ElKatzchen/6DOF-3D-Printed-Robotic-Arm-ROS-2-Computer-Vision-Integration/3D-Printed_Files/SG90S/Pieces/Arm_1st_Joint.SLDPRT

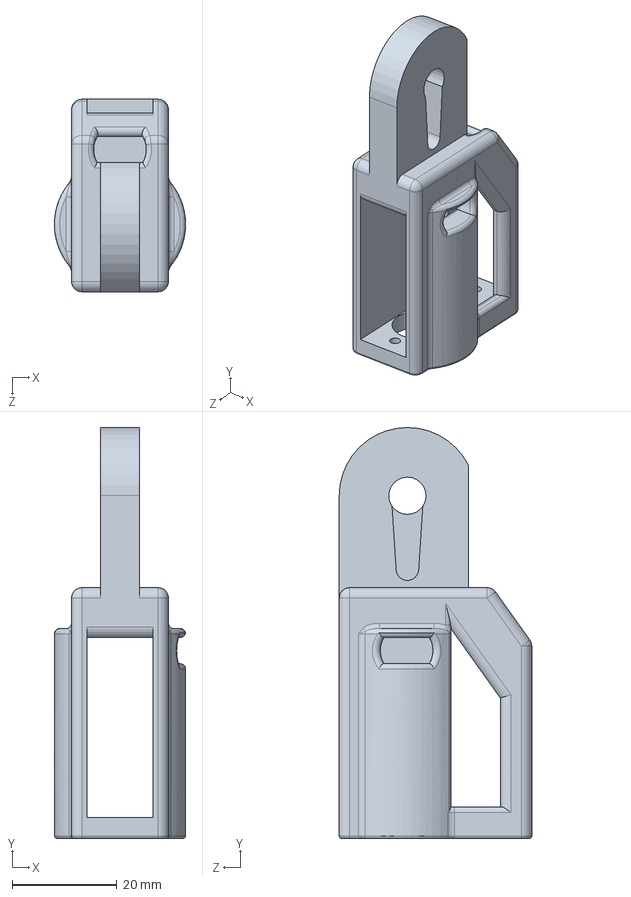
[picture p12: CAD file, 2026-02-13]
3D-Printed_Files/SG90S/Pieces/Arm_1st_Joint.SLDPRT
25.0 x 78.3 x 36.7 mm
