ElKatzchen/6DOF-3D-Printed-Robotic-Arm-ROS-2-Computer-Vision-Integration/3D-Printed_Files/SG90S/STLs/Arm_2nd_Joint.STL

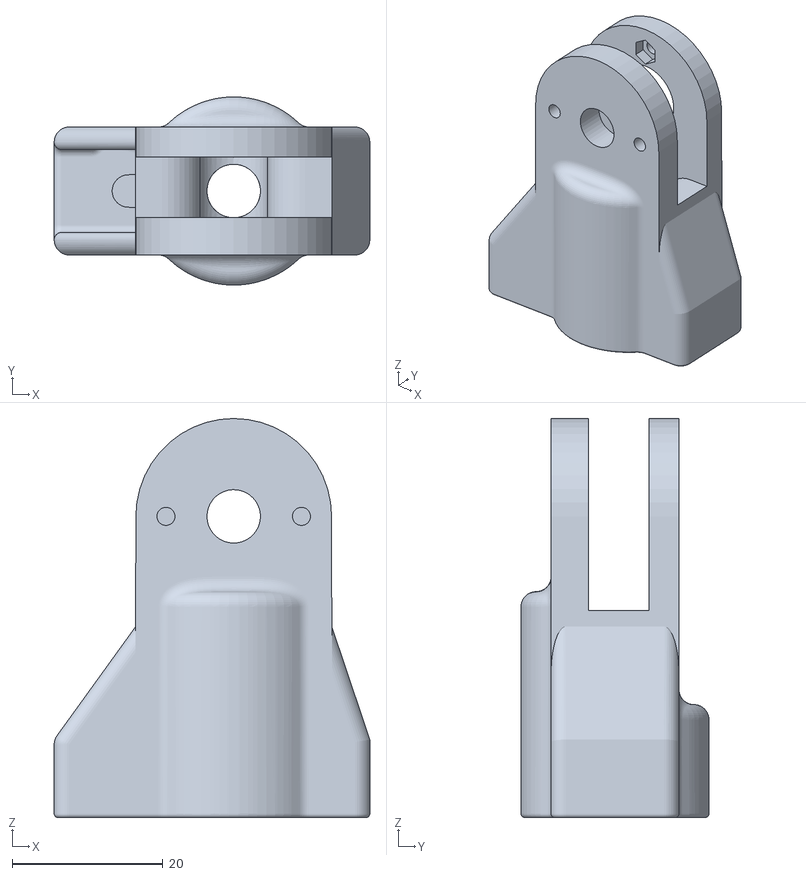
[picture p13: CAD file, 2026-02-13]
3D-Printed_Files/SG90S/STLs/Arm_2nd_Joint.STL
41.9 x 25.0 x 53.0
