ElKatzchen/6DOF-3D-Printed-Robotic-Arm-ROS-2-Computer-Vision-Integration/3D-Printed_Files/ES08MA_II/Pieces/Arm_2nd_Joint.SLDPRT

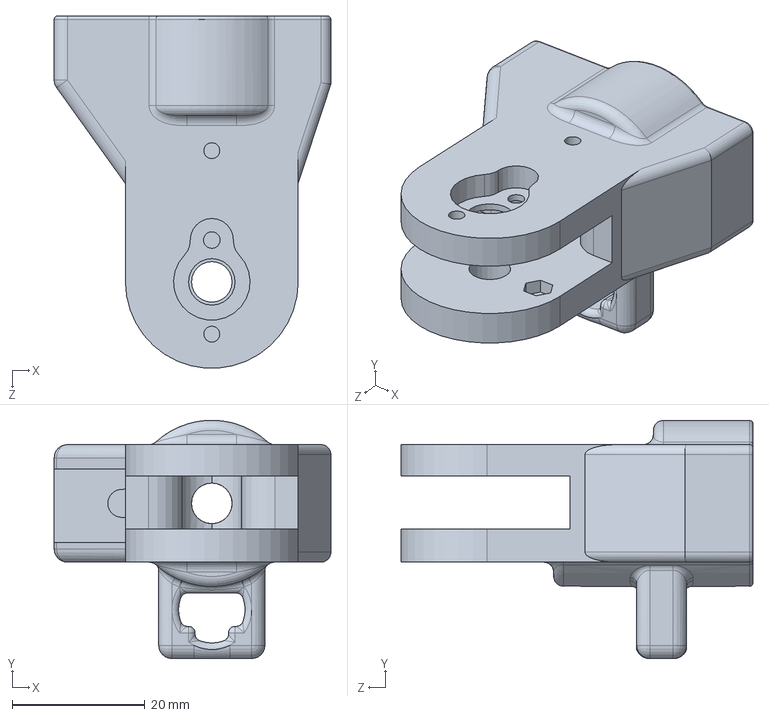
[picture p14: CAD file, 2026-04-28]
3D-Printed_Files/ES08MA_II/Pieces/Arm_2nd_Joint.SLDPRT
41.6 x 35.8 x 53.0 mm
