ElKatzchen/6DOF-3D-Printed-Robotic-Arm-ROS-2-Computer-Vision-Integration/3D-Printed_Files/SG90S/Pieces/Base_Arm_Joint.SLDPRT

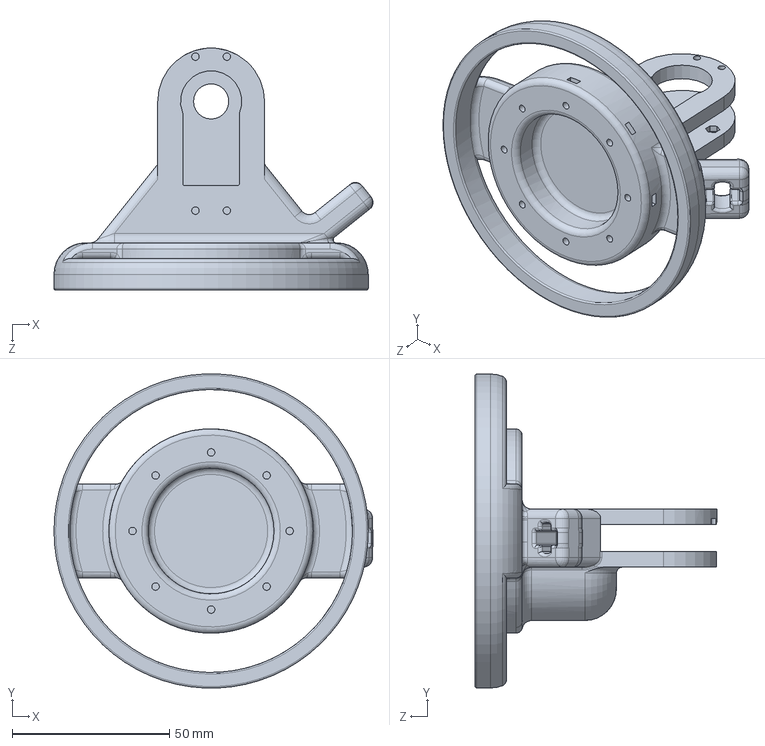
[picture p15: CAD file, 2026-02-13]
3D-Printed_Files/SG90S/Pieces/Base_Arm_Joint.SLDPRT
101.5 x 99.9 x 77.0 mm
