ElKatzchen/6DOF-3D-Printed-Robotic-Arm-ROS-2-Computer-Vision-Integration/3D-Printed_Files/SG90S/STLs/Claw_Finger_Right.STL

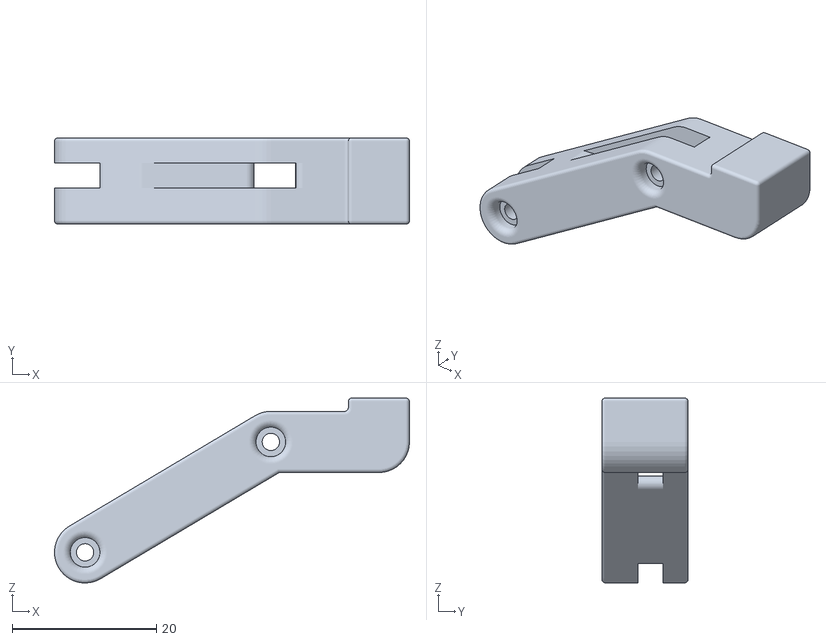
[picture p16: CAD file, 2026-02-13]
3D-Printed_Files/SG90S/STLs/Claw_Finger_Right.STL
49.3 x 12.0 x 25.7
