ElKatzchen/6DOF-3D-Printed-Robotic-Arm-ROS-2-Computer-Vision-Integration/3D-Printed_Files/SG90S/Pieces/Holder_SG90S_T2.SLDPRT

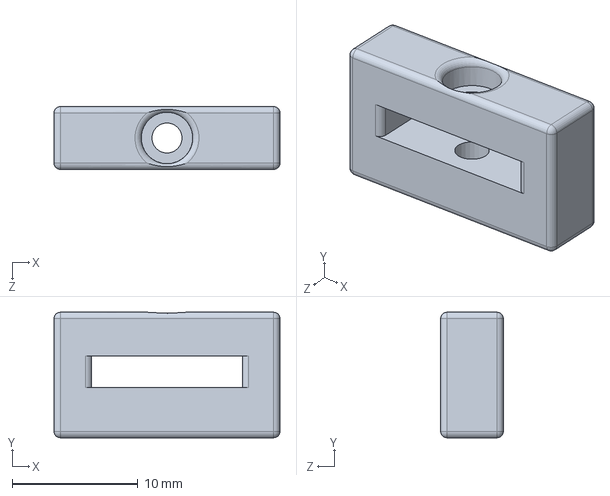
[picture p17: CAD file, 2026-02-13]
3D-Printed_Files/SG90S/Pieces/Holder_SG90S_T2.SLDPRT
18.0 x 10.0 x 5.00 mm
