ElKatzchen/6DOF-3D-Printed-Robotic-Arm-ROS-2-Computer-Vision-Integration/3D-Printed_Files/SG90S/STLs/Holder_SG90S_T1.STL

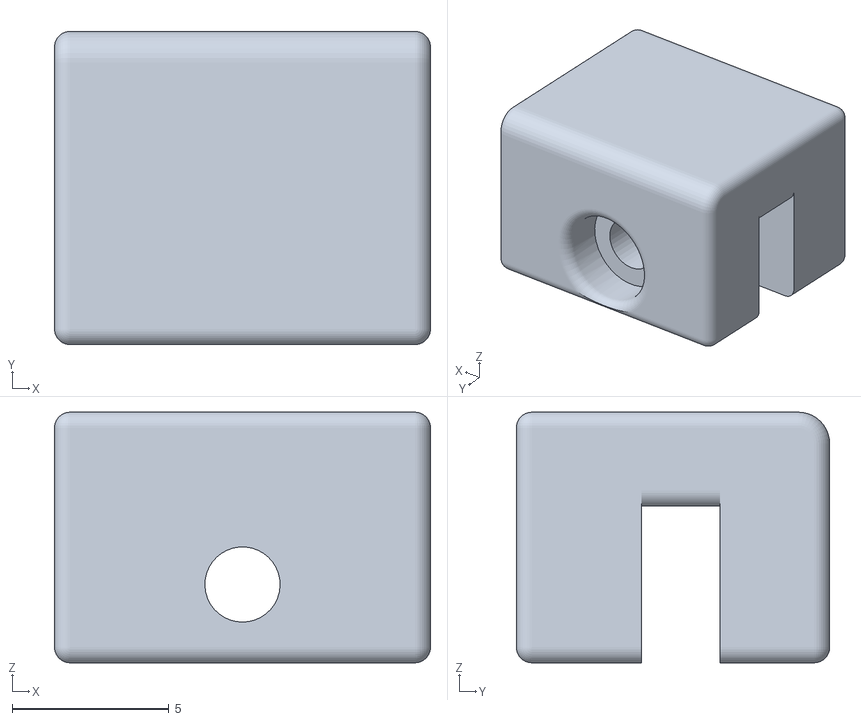
[picture p18: CAD file, 2026-02-13]
3D-Printed_Files/SG90S/STLs/Holder_SG90S_T1.STL
12.0 x 10.0 x 8.00
