ElKatzchen/6DOF-3D-Printed-Robotic-Arm-ROS-2-Computer-Vision-Integration/3D-Printed_Files/ES08MA_II/Pieces/Holder_MG996R_Rotor.SLDPRT

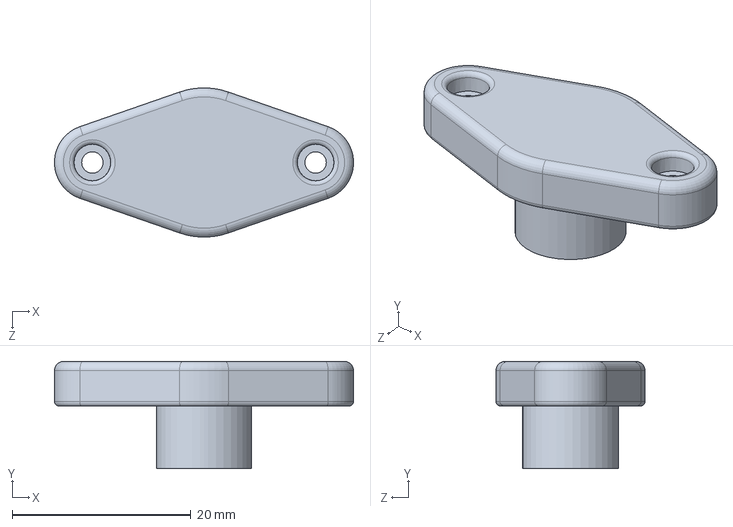
[picture p19: CAD file, 2026-02-13]
3D-Printed_Files/ES08MA_II/Pieces/Holder_MG996R_Rotor.SLDPRT
33.5 x 12.0 x 16.7 mm
