ElKatzchen/6DOF-3D-Printed-Robotic-Arm-ROS-2-Computer-Vision-Integration/3D-Printed_Files/ES08MA_II/STLs/Base_Rotor_Plate.STL

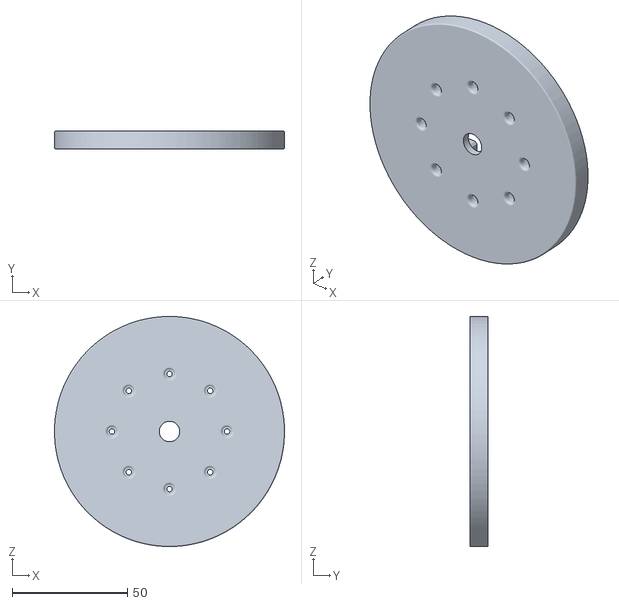
[picture p20: CAD file, 2026-02-13]
3D-Printed_Files/ES08MA_II/STLs/Base_Rotor_Plate.STL
100.0 x 8.00 x 100.0
