ElKatzchen/6DOF-3D-Printed-Robotic-Arm-ROS-2-Computer-Vision-Integration/3D-Printed_Files/ES08MA_II/STLs/Claw_Gear_Joint.STL

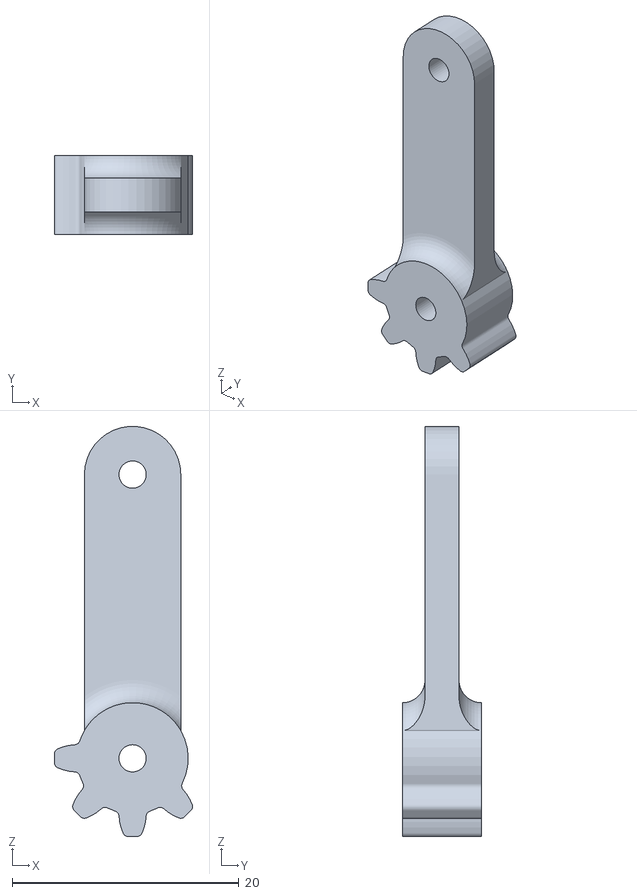
[picture p22: CAD file, 2026-02-13]
3D-Printed_Files/ES08MA_II/STLs/Claw_Gear_Joint.STL
12.2 x 7.00 x 36.1
