ElKatzchen/6DOF-3D-Printed-Robotic-Arm-ROS-2-Computer-Vision-Integration/3D-Printed_Files/SG90S/Pieces/Holder_SG90S_Rotor.SLDPRT

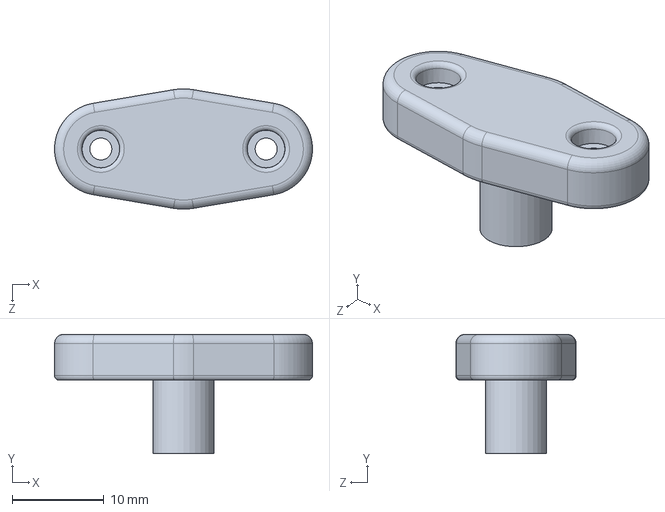
[picture p25: CAD file, 2026-02-13]
3D-Printed_Files/SG90S/Pieces/Holder_SG90S_Rotor.SLDPRT
28.1 x 13.0 x 13.1 mm
