ElKatzchen/6DOF-3D-Printed-Robotic-Arm-ROS-2-Computer-Vision-Integration/3D-Printed_Files/ES08MA_II/STLs/Claw_Joint.STL

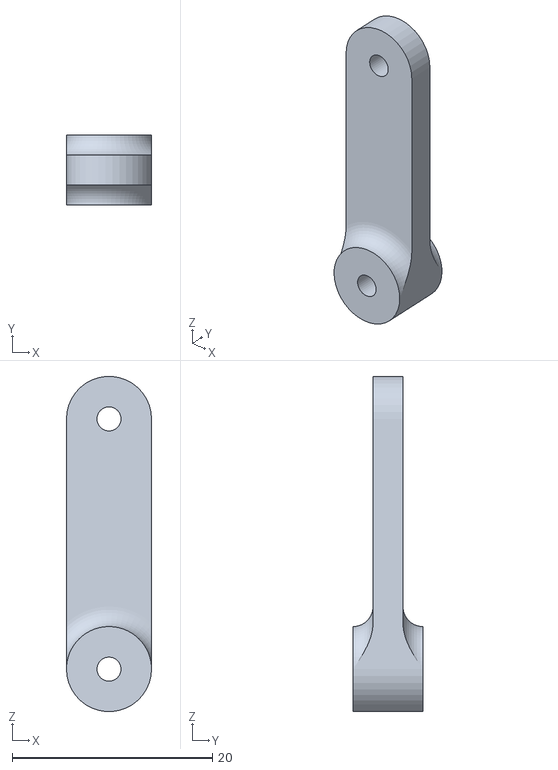
[picture p26: CAD file, 2026-02-13]
3D-Printed_Files/ES08MA_II/STLs/Claw_Joint.STL
8.50 x 7.00 x 33.5
