ElKatzchen/6DOF-3D-Printed-Robotic-Arm-ROS-2-Computer-Vision-Integration/3D-Printed_Files/SG90S/STLs/Claw_Gear_Motor_Joint.STL

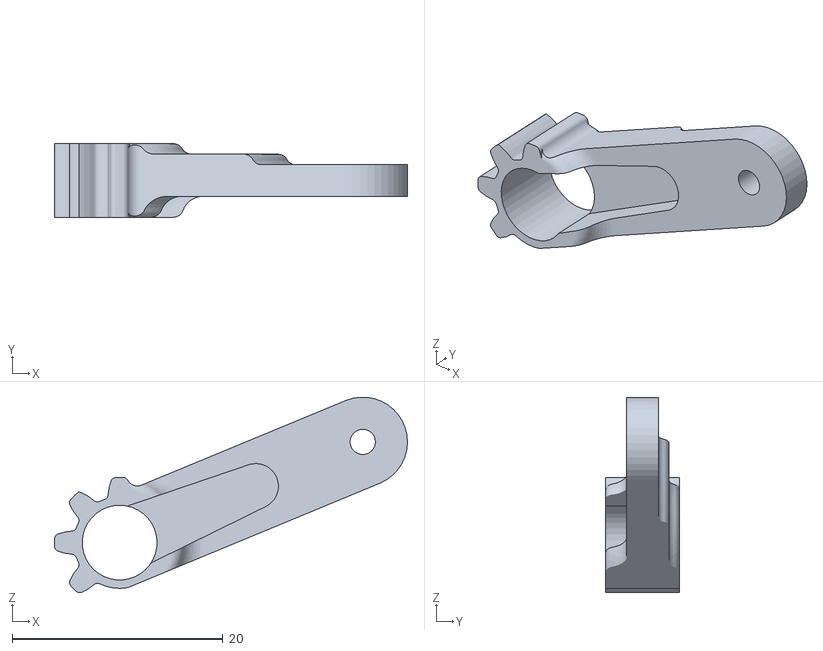
[picture p27: CAD file, 2026-02-13]
3D-Printed_Files/SG90S/STLs/Claw_Gear_Motor_Joint.STL
33.5 x 7.00 x 18.6
