ElKatzchen/6DOF-3D-Printed-Robotic-Arm-ROS-2-Computer-Vision-Integration/3D-Printed_Files/ES08MA_II/STLs/Base_Box_Joint.STL

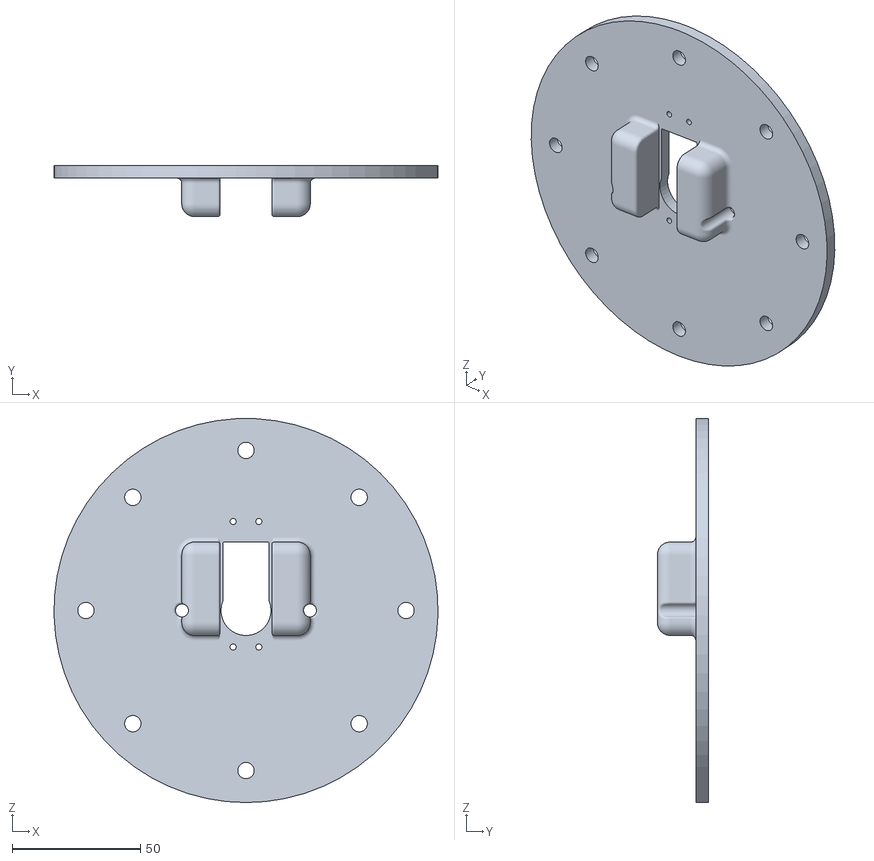
[picture p28: CAD file, 2026-02-13]
3D-Printed_Files/ES08MA_II/STLs/Base_Box_Joint.STL
150.0 x 20.0 x 150.0
