ElKatzchen/6DOF-3D-Printed-Robotic-Arm-ROS-2-Computer-Vision-Integration/3D-Printed_Files/ES08MA_II/STLs/Holder_MG996R_Lower.STL

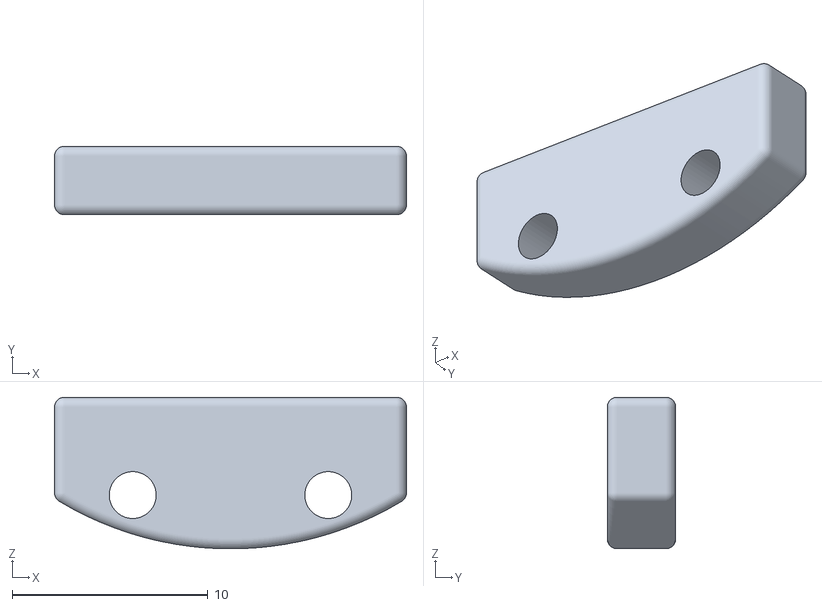
[picture p29: CAD file, 2026-02-13]
3D-Printed_Files/ES08MA_II/STLs/Holder_MG996R_Lower.STL
18.0 x 3.50 x 7.74
