ElKatzchen/6DOF-3D-Printed-Robotic-Arm-ROS-2-Computer-Vision-Integration/3D-Printed_Files/ES08MA_II/Pieces/Holder_ES08MA_II_T2.SLDPRT

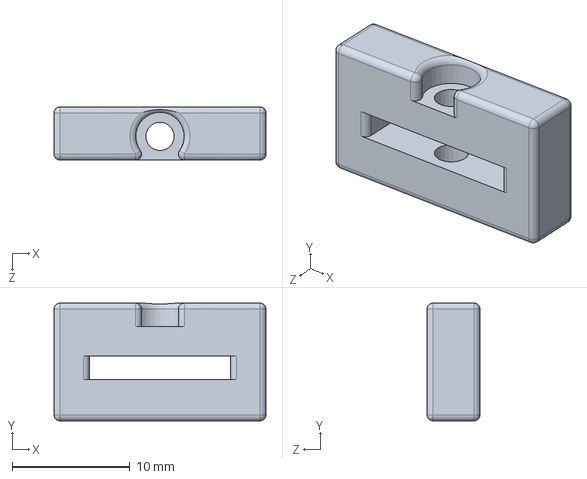
[picture p30: CAD file, 2026-02-13]
3D-Printed_Files/ES08MA_II/Pieces/Holder_ES08MA_II_T2.SLDPRT
18.0 x 10.0 x 4.50 mm
