ElKatzchen/6DOF-3D-Printed-Robotic-Arm-ROS-2-Computer-Vision-Integration/3D-Printed_Files/ES08MA_II/Pieces/Claw_Hand.SLDPRT

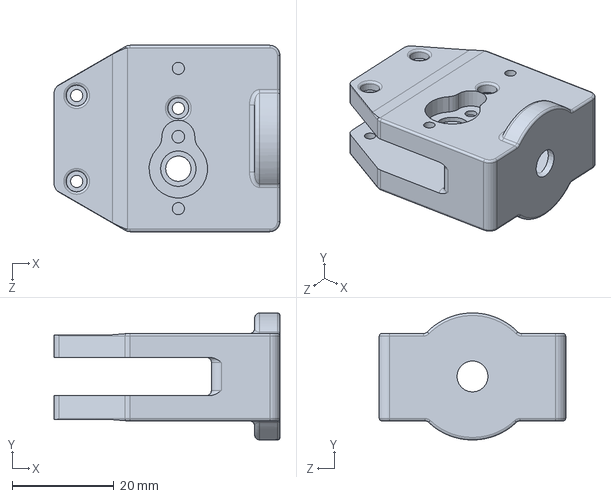
[picture p31: CAD file, 2026-02-13]
3D-Printed_Files/ES08MA_II/Pieces/Claw_Hand.SLDPRT
44.5 x 25.0 x 36.7 mm
